arithmaldor/Nintendo-Breakout/Photos/20190725_023706.jpg

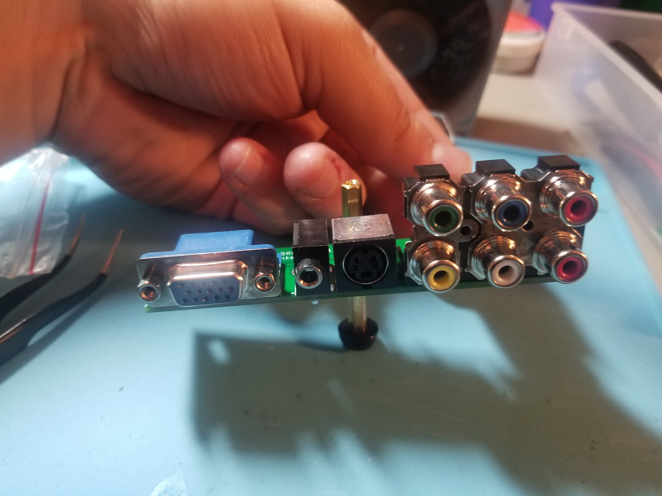
Photos/20190725_023706.jpg
